joshajohnson/entropy/mechanicals/entropy-case-0.3/plate.dxf

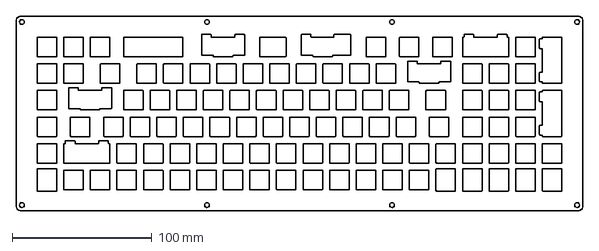
[picture p26: CAD file, 2021-12-18]
mechanicals/entropy-case-0.3/plate.dxf
405.9 x 139.3 mm
