joshajohnson/entropy/mechanicals/entropy-case-0.3/plate+1.dxf

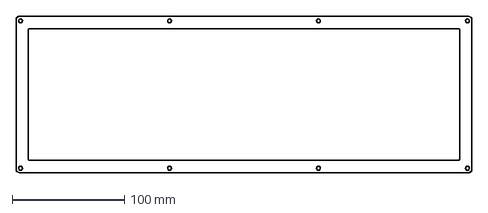
[picture p27: CAD file, 2021-12-18]
mechanicals/entropy-case-0.3/plate+1.dxf
405.9 x 139.3 mm
