joshajohnson/entropy/hardware/0.1/keyboard.sch

## KiCad design hardware/0.1/keyboard.sch (2020-07-07)

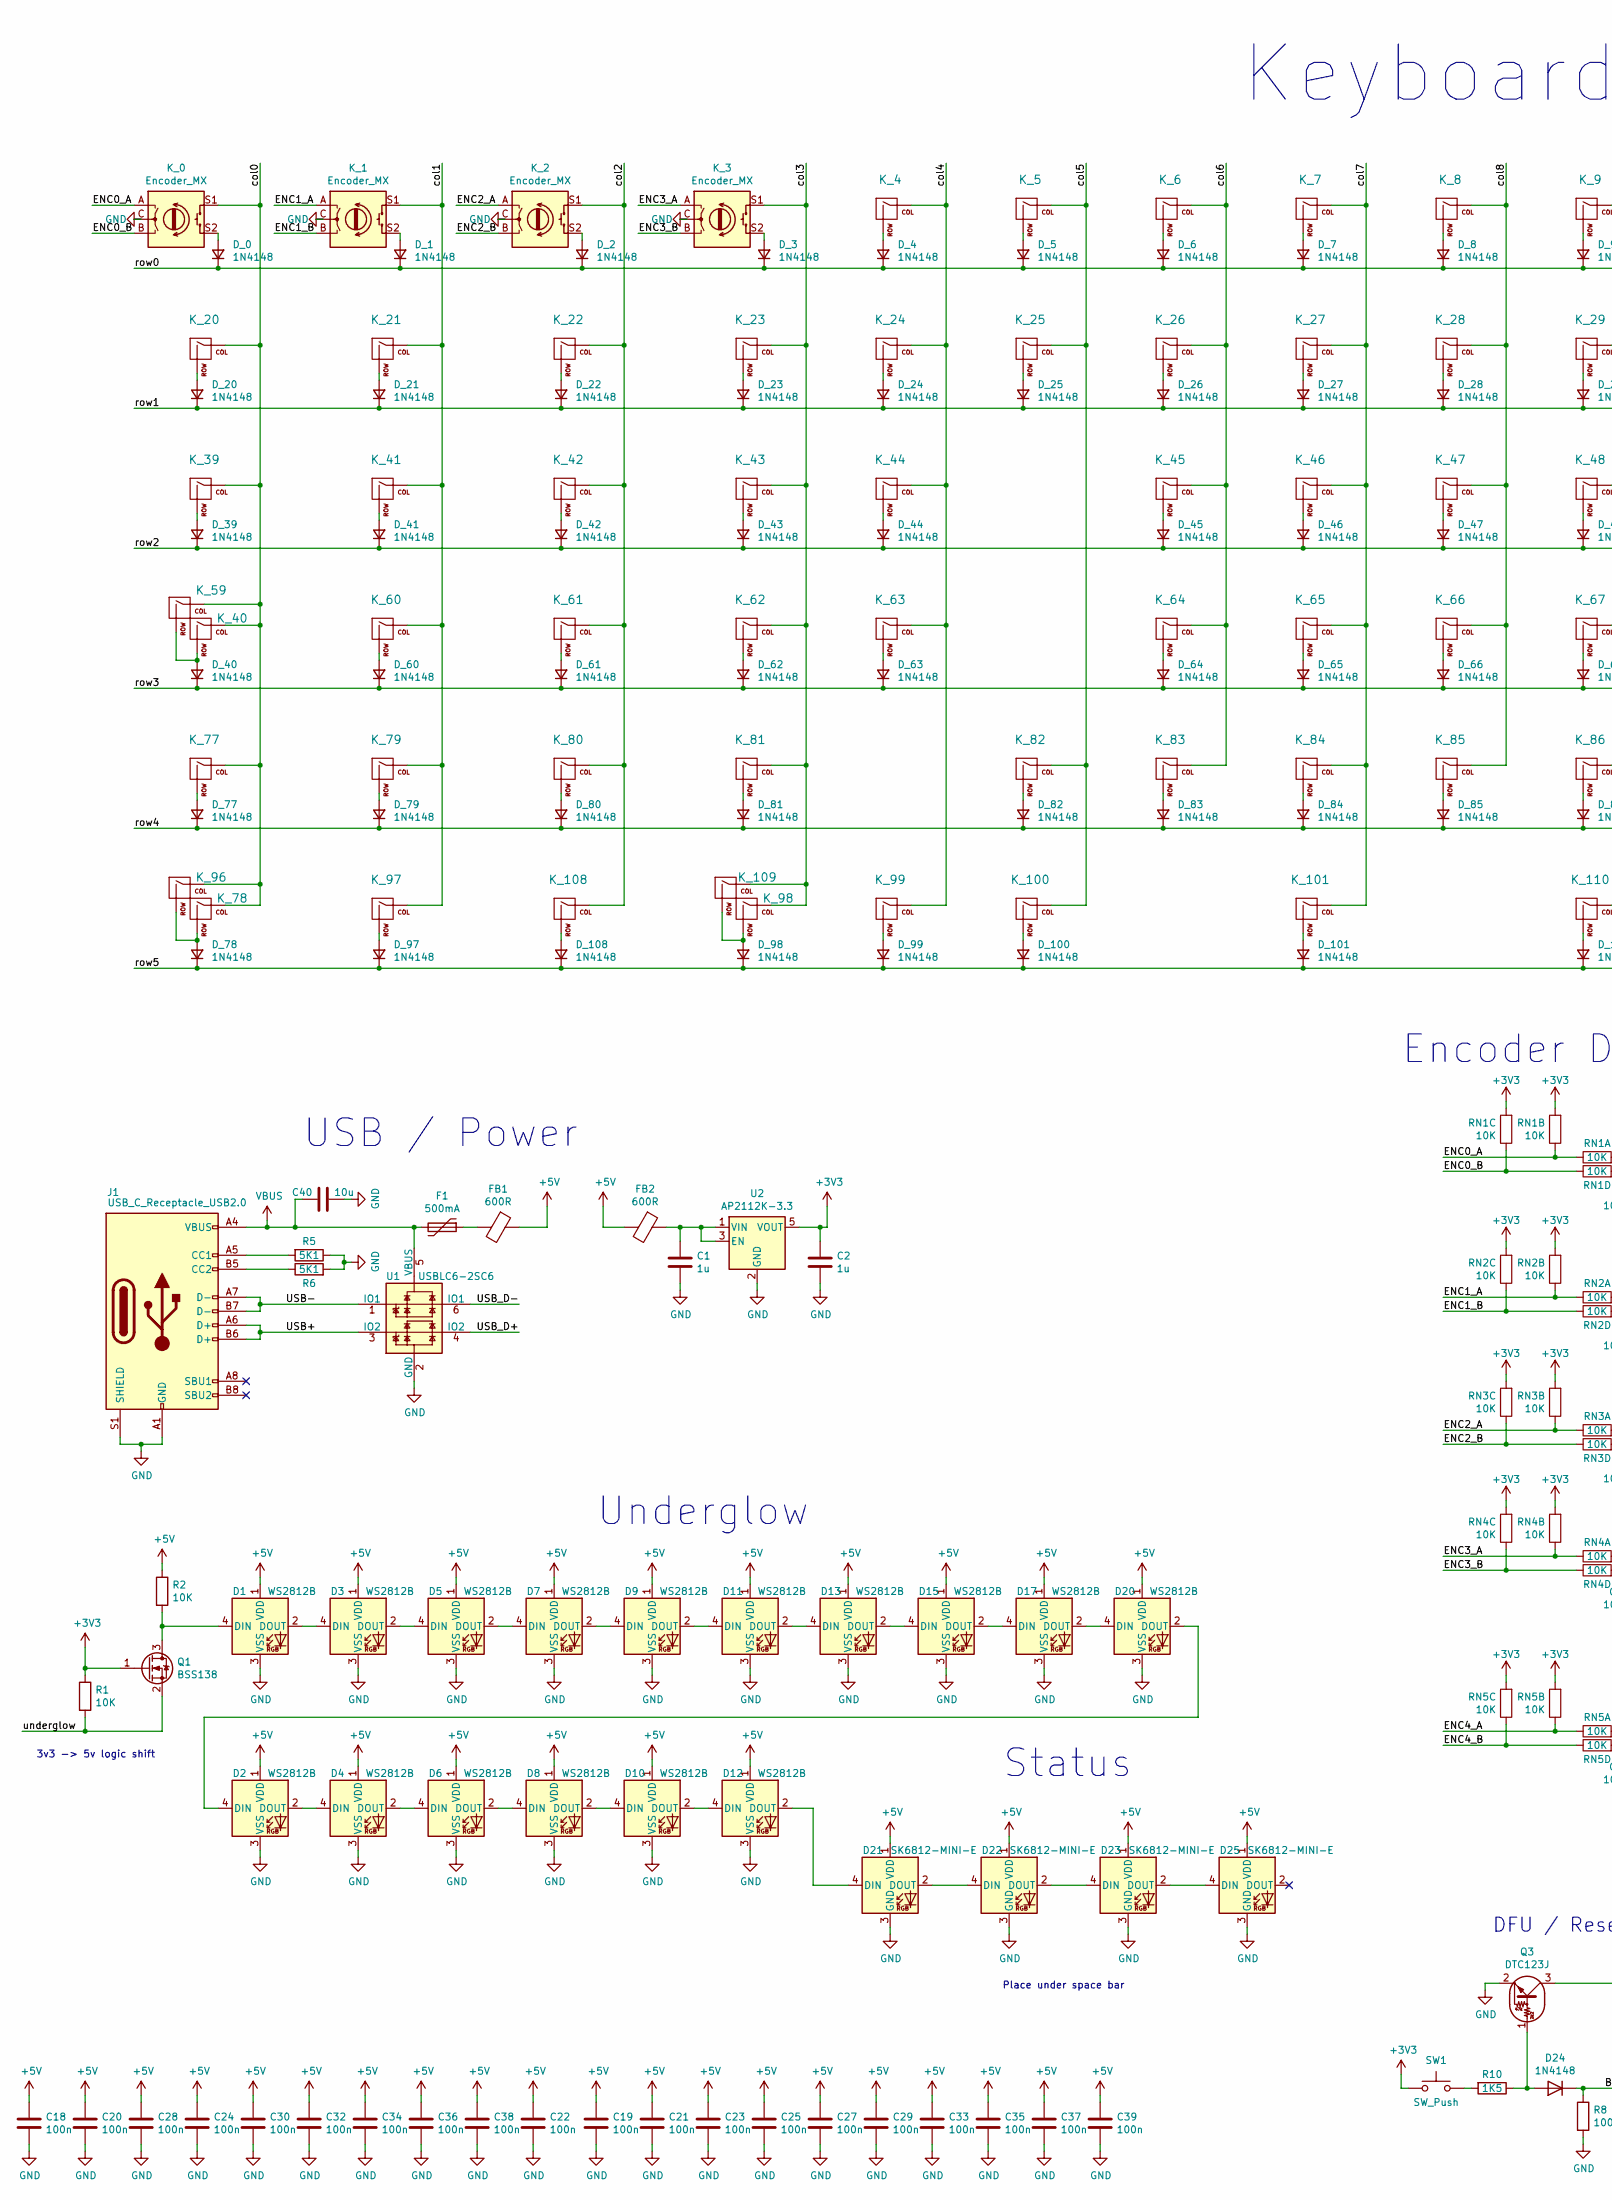
[picture p30: schematic keyboard.sch, part in row 1, column 1]

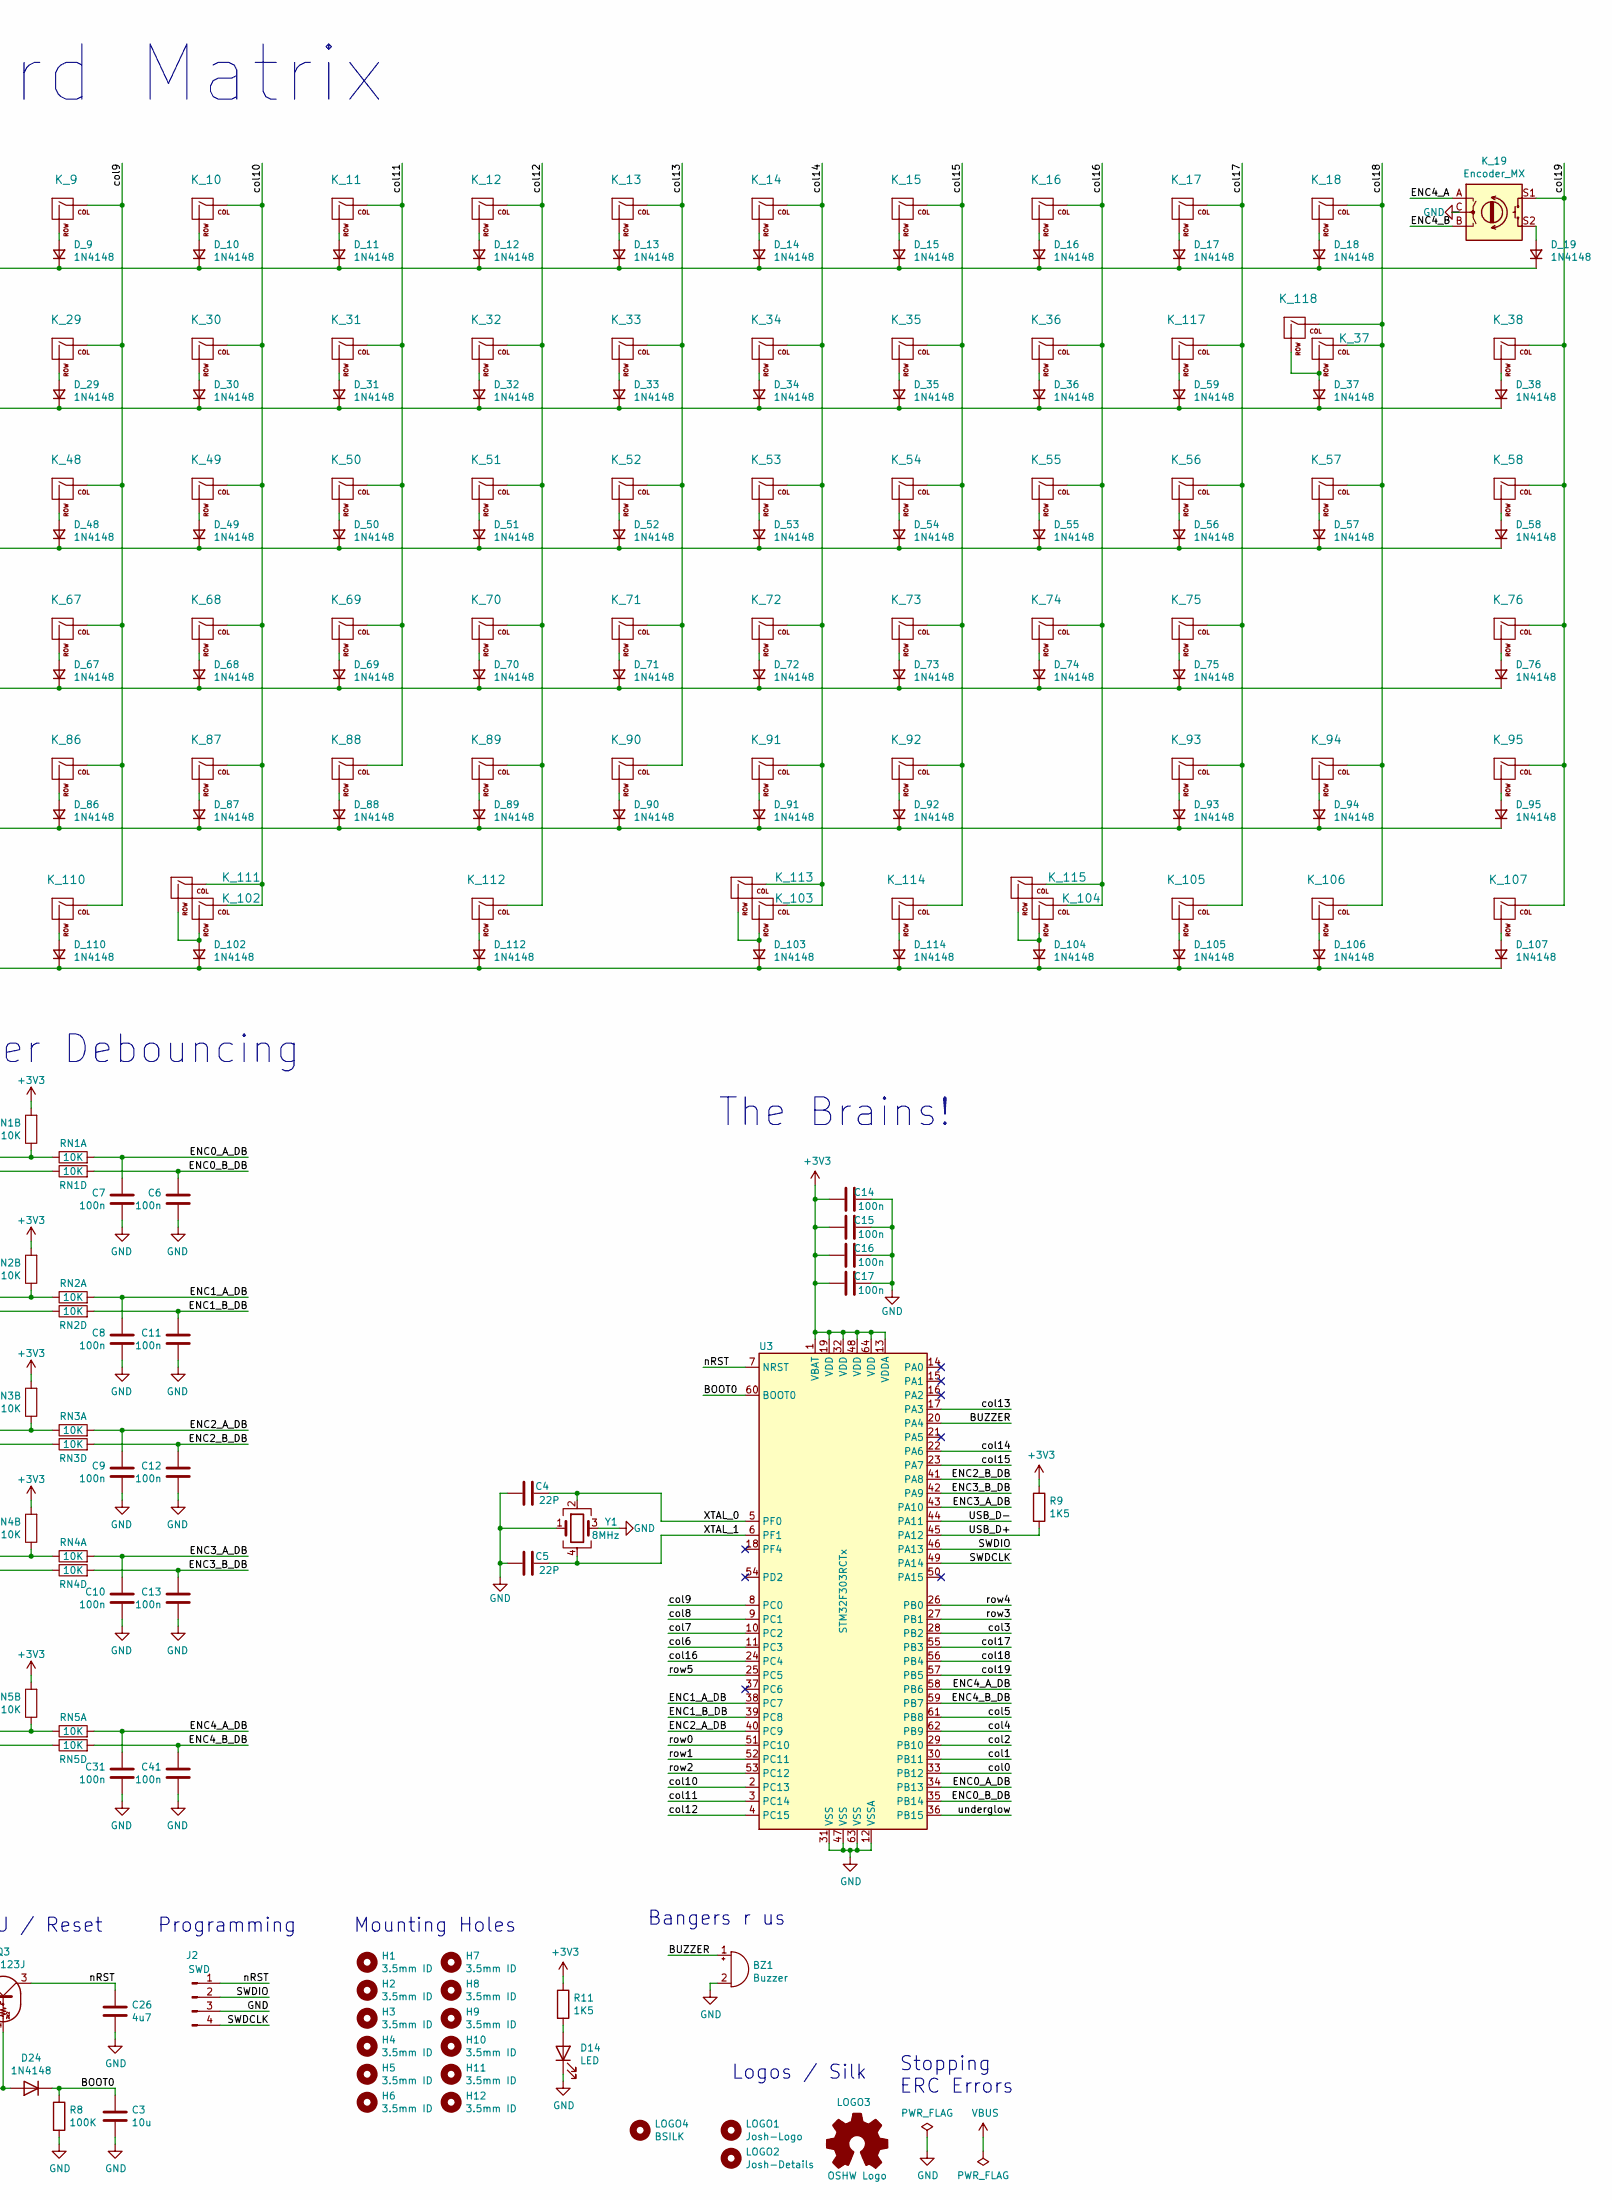
[picture p31: schematic keyboard.sch, part in row 1, column 2]

Parts:
BZ1: Buzzer; Buzzer_Murata_PKMCS0909E4000-R1
C1, C2: 1u; C_0603_1608Metric; MPN CL10A105MP8NNNC; LCSC C15849
C3, C40: 10u; C_0603_1608Metric; JLCSMT 1740133
C4, C5: 22P; C_0603_1608Metric; MPN CL10C220JB8NNNC; JLCSMT C1653
C6, C7, C8, C9, C10, C11, C12, C13, C14, C15, C16, C17, C31, C41: 100n; C_0603_1608Metric; MPN CC0603KRX7R9BB104; JLCSMT C14663
C18, C19, C20, C21, C22, C23, C24, C25, C27, C28, C29, C30, C32, C33, C34, C35, C36, C37, C38, C39: 100n; C_0603_1608Metric; MPN CC0603KRX7R9BB104; LCSC C14663
C26: 4u7; C_0603_1608Metric; MPN CL10A475KO8NNNC; JLCSMT C19666
D1, D2, D3, D4, D5, D6, D7, D8, D9, D10, D11, D12, D13, D15, D17, D20: WS2812B; LED_WS2812B_PLCC4_5.0x5.0mm_P3.2mm; MPN WS2812B-B; DigiKey 1528-1104-ND
D14: LED; LED_0603_1608Metric
D21, D22, D23, D25: SK6812-MINI-E; SK8612-MINI-E
D24: 1N4148; D_SOD-123; MPN 1N4148W; JLCSMT C81598
D_0, D_1, D_2, D_3, D_4, D_5, D_6, D_7, D_8, D_9, D_10, D_11, D_12, D_13, D_14, D_15, D_16, D_17, D_18, D_19, D_20, D_21, D_22, D_23, D_24, D_25, D_26, D_27, D_28, D_29, D_30, D_31, D_32, D_33, D_34, D_35, D_36, D_37, D_38, D_39, D_40, D_41, D_42, D_43, D_44, D_45, D_46, D_47, D_48, D_49, D_50, D_51, D_52, D_53, D_54, D_55, D_56, D_57, D_58, D_59, D_60, D_61, D_62, D_63, D_64, D_65, D_66, D_67, D_68, D_69, D_70, D_71, D_72, D_73, D_74, D_75, D_76, D_77, D_78, D_79, D_80, D_81, D_82, D_83, D_84, D_85, D_86, D_87, D_88, D_89, D_90, D_91, D_92, D_93, D_94, D_95, D_97, D_98, D_99, D_100, D_101, D_102, D_103, D_104, D_105, D_106, D_107, D_108, D_110, D_112, D_114: 1N4148; D_SOD-123; MPN 1N4148W; JLCSMT C81598
F1: 500mA; Fuse_0805_2012Metric
FB1, FB2: 600R; Ferrite_Bead_0603
H1, H2, H3, H4, H5, H6, H7, H8, H9, H10, H11, H12: 3.5mm ID; MountingHole_3.5mm
J1: USB_C_Receptacle_USB2.0; USB_C_U262-161N-4BVC11; MPN U262-161N-4BVC11; LCSC C319148
J2: SWD; STM_4_PIN_THT_Staggered
K_0, K_1, K_2, K_3, K_19: Encoder_MX; MX_KEYSWITCH_ENCODER
K_4, K_5, K_6, K_7, K_8, K_9, K_10, K_11, K_12, K_13, K_14, K_15, K_16, K_17, K_18, K_20, K_21, K_22, K_23, K_24, K_25, K_26, K_27, K_28, K_29, K_30, K_31, K_32, K_33, K_34, K_35, K_36, K_38, K_39, K_41, K_42, K_43, K_45, K_46, K_47, K_48, K_49, K_50, K_51, K_52, K_53, K_54, K_55, K_56, K_58, K_59, K_60, K_61, K_62, K_64, K_65, K_66, K_67, K_68, K_69, K_70, K_71, K_72, K_73, K_74, K_76, K_77, K_79, K_80, K_81, K_83, K_84, K_85, K_86, K_87, K_88, K_89, K_90, K_91, K_92, K_94, K_95, K_96, K_97, K_105, K_106, K_107, K_108, K_109, K_113, K_114, K_115, K_117, K_118: KEYSW; MXOnly-1U-NoLED
K_37, K_40, K_78: KEYSW; MXOnly-2U-NoLED
K_44, K_57, K_103, K_104: KEYSW; MXOnly-1.5U-NoLED
K_63, K_93: KEYSW; MXOnly-1.75U-NoLED
K_75, K_82, K_112: KEYSW; MXOnly-2.25U-ReversedStabilizers-NoLED
K_98: KEYSW; MXOnly-2U-ReversedStabilizers-NoLED
K_99, K_100, K_101, K_111: KEYSW; MXOnly-1.25U-NoLED
K_102: KEYSW; MXOnly-6.25U-ReversedStabilizers-NoLED
K_110: KEYSW; MXOnly-2.75U-ReversedStabilizers-NoLED
LOGO1: Josh-Logo; josh-johnson-logo-17x3
LOGO2: Josh-Details; josh-details
LOGO3: OSHW Logo; OSHW_Logo_3.6x3.6_F.Mask
LOGO4: BSILK; back_silk_v0
Q1: BSS138; SOT-23; MPN BSS138P,215; LCSC C75547
Q3: DTC123J; SOT-23
R1, R2: 10K; R_0603_1608Metric; MPN 0603WAF1002T5E; LCSC C25804
R5, R6: 5K1; R_0603_1608Metric; MPN 0603WAF5101T5E; JLCSMT C23186
R8: 100K; R_0603_1608Metric; MPN 0603WAF1003T5E; JLCSMT C25803
R9, R10, R11: 1K5; R_0603_1608Metric; MPN 0603WAF1501T5E; JLCSMT C22843
RN1, RN2, RN3, RN4, RN5: 10K; R_Array_Convex_4x0603; MPN 4D03WGJ0103T5E; JLCSMT C29718
SW1: SW_Push; Panasonic_EVQPUL_EVQPUC
U1: USBLC6-2SC6; SOT-23-6
U2: AP2112K-3.3; SOT-23-5; MPN AP2112K-3.3TRG1; LCSC C51118
U3: STM32F303RCTx; LQFP-64_10x10mm_P0.5mm; MPN STM32F303RCT6; JLCSMT C65361
Y1: 8MHz; Crystal_SMD_3225-4Pin_3.2x2.5mm

Connections:
+3V3: C2.2, C14.2, C15.2, C16.2, C17.2, Q1.1 (G), R1.1, R9.1, R11.1, RN1.2, RN1.3, RN2.2, RN2.3, RN3.2, RN3.3, RN4.2, RN4.3, RN5.2, RN5.3, SW1.1, U2.5 (VOUT), U3.1 (VBAT), U3.13 (VDDA), U3.19 (VDD), U3.32 (VDD), U3.48 (VDD), U3.64 (VDD)
+5V: C18.2, C19.2, C20.2, C21.2, C22.2, C23.2, C24.2, C25.2, C27.2, C28.2, C29.2, C30.2, C32.2, C33.2, C34.2, C35.2, C36.2, C37.2, C38.2, C39.2, D1.1 (VDD), D2.1 (VDD), D3.1 (VDD), D4.1 (VDD), D5.1 (VDD), D6.1 (VDD), D7.1 (VDD), D8.1 (VDD), D9.1 (VDD), D10.1 (VDD), D11.1 (VDD), D12.1 (VDD), D13.1 (VDD), D15.1 (VDD), D17.1 (VDD), D20.1 (VDD), D21.1 (VDD), D22.1 (VDD), D23.1 (VDD), D25.1 (VDD), FB1.1, FB2.2, R2.1
BOOT0: C3.1, D24.1 (K), R8.1, U3.60 (BOOT0)
BUZZER: BZ1.1 (-), U3.20 (PA4)
ENC0_A: K_0.A, RN1.5, RN1.6
ENC0_A_DB: C7.1, RN1.4, U3.34 (PB13)
ENC0_B: K_0.B, RN1.7, RN1.8
ENC0_B_DB: C6.1, RN1.1, U3.35 (PB14)
ENC1_A: K_1.A, RN2.5, RN2.6
ENC1_A_DB: C8.1, RN2.4, U3.38 (PC7)
ENC1_B: K_1.B, RN2.7, RN2.8
ENC1_B_DB: C11.1, RN2.1, U3.39 (PC8)
ENC2_A: K_2.A, RN3.5, RN3.6
ENC2_A_DB: C9.1, RN3.4, U3.40 (PC9)
ENC2_B: K_2.B, RN3.7, RN3.8
ENC2_B_DB: C12.1, RN3.1, U3.41 (PA8)
ENC3_A: K_3.A, RN4.5, RN4.6
ENC3_A_DB: C10.1, RN4.4, U3.43 (PA10)
ENC3_B: K_3.B, RN4.7, RN4.8
ENC3_B_DB: C13.1, RN4.1, U3.42 (PA9)
ENC4_A: K_19.A, RN5.5, RN5.6
ENC4_A_DB: C31.1, RN5.4, U3.58 (PB6)
ENC4_B: K_19.B, RN5.7, RN5.8
ENC4_B_DB: C41.1, RN5.1, U3.59 (PB7)
GND: BZ1.2 (+), C1.1, C2.1, C3.2, C4.2, C5.2, C6.2, C7.2, C8.2, C9.2, C10.2, C11.2, C12.2, C13.2, C14.1, C15.1, C16.1, C17.1, C18.1, C19.1, C20.1, C21.1, C22.1, C23.1, C24.1, C25.1, C26.2, C27.1, C28.1, C29.1, C30.1, C31.2, C32.1, C33.1, C34.1, C35.1, C36.1, C37.1, C38.1, C39.1, C40.1, C41.2, D1.3 (VSS), D2.3 (VSS), D3.3 (VSS), D4.3 (VSS), D5.3 (VSS), D6.3 (VSS), D7.3 (VSS), D8.3 (VSS), D9.3 (VSS), D10.3 (VSS), D11.3 (VSS), D12.3 (VSS), D13.3 (VSS), D14.1 (K), D15.3 (VSS), D17.3 (VSS), D20.3 (VSS), D21.3 (GND), D22.3 (GND), D23.3 (GND), D25.3 (GND), J1.A1 (GND), J1.A12 (GND), J1.B1 (GND), J1.B12 (GND), J1.S1 (SHIELD), J2.3, K_0.C, K_1.C, K_2.C, K_3.C, K_19.C, Q3.2 (E), R5.1, R6.2, R8.2, U1.2 (GND), U2.2 (GND), U3.12 (VSSA), U3.31 (VSS), U3.47 (VSS), U3.63 (VSS), Y1.1, Y1.3
unnamed: C1.2, FB2.1, U2.1 (VIN), U2.3 (EN)
unnamed: D1.2 (DOUT), D3.4 (DIN)
unnamed: D1.4 (DIN), Q1.3 (D), R2.2
unnamed: D2.2 (DOUT), D4.4 (DIN)
unnamed: D2.4 (DIN), D20.2 (DOUT)
unnamed: D3.2 (DOUT), D5.4 (DIN)
unnamed: D4.2 (DOUT), D6.4 (DIN)
unnamed: D5.2 (DOUT), D7.4 (DIN)
unnamed: D6.2 (DOUT), D8.4 (DIN)
unnamed: D7.2 (DOUT), D9.4 (DIN)
unnamed: D10.2 (DOUT), D12.4 (DIN)
unnamed: D8.2 (DOUT), D10.4 (DIN)
unnamed: D11.2 (DOUT), D13.4 (DIN)
unnamed: D9.2 (DOUT), D11.4 (DIN)
unnamed: D12.2 (DOUT), D21.4 (DIN)
unnamed: D13.2 (DOUT), D15.4 (DIN)
unnamed: D14.2 (A), R11.2
unnamed: D15.2 (DOUT), D17.4 (DIN)
unnamed: D17.2 (DOUT), D20.4 (DIN)
unnamed: D21.2 (DOUT), D22.4 (DIN)
unnamed: D22.2 (DOUT), D23.4 (DIN)
unnamed: D23.2 (DOUT), D25.4 (DIN)
unnamed: D24.2 (A), Q3.1 (B), R10.1
unnamed: D_0.2 (A), K_0.S2
unnamed: D_1.2 (A), K_1.S2
unnamed: D_2.2 (A), K_2.S2
unnamed: D_3.2 (A), K_3.S2
unnamed: D_4.2 (A), K_4.2 (ROW)
unnamed: D_5.2 (A), K_5.2 (ROW)
unnamed: D_6.2 (A), K_6.2 (ROW)
unnamed: D_7.2 (A), K_7.2 (ROW)
unnamed: D_8.2 (A), K_8.2 (ROW)
unnamed: D_9.2 (A), K_9.2 (ROW)
unnamed: D_10.2 (A), K_10.2 (ROW)
unnamed: D_11.2 (A), K_11.2 (ROW)
unnamed: D_12.2 (A), K_12.2 (ROW)
unnamed: D_13.2 (A), K_13.2 (ROW)
unnamed: D_14.2 (A), K_14.2 (ROW)
unnamed: D_15.2 (A), K_15.2 (ROW)
unnamed: D_16.2 (A), K_16.2 (ROW)
unnamed: D_17.2 (A), K_17.2 (ROW)
unnamed: D_18.2 (A), K_18.2 (ROW)
unnamed: D_19.2 (A), K_19.S2
unnamed: D_20.2 (A), K_20.2 (ROW)
unnamed: D_21.2 (A), K_21.2 (ROW)
unnamed: D_22.2 (A), K_22.2 (ROW)
unnamed: D_23.2 (A), K_23.2 (ROW)
unnamed: D_24.2 (A), K_24.2 (ROW)
unnamed: D_25.2 (A), K_25.2 (ROW)
unnamed: D_26.2 (A), K_26.2 (ROW)
unnamed: D_27.2 (A), K_27.2 (ROW)
unnamed: D_28.2 (A), K_28.2 (ROW)
unnamed: D_29.2 (A), K_29.2 (ROW)
unnamed: D_30.2 (A), K_30.2 (ROW)
unnamed: D_31.2 (A), K_31.2 (ROW)
unnamed: D_32.2 (A), K_32.2 (ROW)
unnamed: D_33.2 (A), K_33.2 (ROW)
unnamed: D_34.2 (A), K_34.2 (ROW)
unnamed: D_35.2 (A), K_35.2 (ROW)
unnamed: D_36.2 (A), K_36.2 (ROW)
unnamed: D_37.2 (A), K_37.2 (ROW), K_118.2 (ROW)
unnamed: D_38.2 (A), K_38.2 (ROW)
unnamed: D_39.2 (A), K_39.2 (ROW)
unnamed: D_40.2 (A), K_40.2 (ROW), K_59.2 (ROW)
unnamed: D_41.2 (A), K_41.2 (ROW)
unnamed: D_42.2 (A), K_42.2 (ROW)
unnamed: D_43.2 (A), K_43.2 (ROW)
unnamed: D_44.2 (A), K_44.2 (ROW)
unnamed: D_45.2 (A), K_45.2 (ROW)
unnamed: D_46.2 (A), K_46.2 (ROW)
unnamed: D_47.2 (A), K_47.2 (ROW)
unnamed: D_48.2 (A), K_48.2 (ROW)
unnamed: D_49.2 (A), K_49.2 (ROW)
unnamed: D_50.2 (A), K_50.2 (ROW)
unnamed: D_51.2 (A), K_51.2 (ROW)
unnamed: D_52.2 (A), K_52.2 (ROW)
unnamed: D_53.2 (A), K_53.2 (ROW)
unnamed: D_54.2 (A), K_54.2 (ROW)
unnamed: D_55.2 (A), K_55.2 (ROW)
unnamed: D_56.2 (A), K_56.2 (ROW)
unnamed: D_57.2 (A), K_57.2 (ROW)
unnamed: D_58.2 (A), K_58.2 (ROW)
unnamed: D_59.2 (A), K_117.2 (ROW)
unnamed: D_60.2 (A), K_60.2 (ROW)
unnamed: D_61.2 (A), K_61.2 (ROW)
unnamed: D_62.2 (A), K_62.2 (ROW)
unnamed: D_63.2 (A), K_63.2 (ROW)
unnamed: D_64.2 (A), K_64.2 (ROW)
unnamed: D_65.2 (A), K_65.2 (ROW)
unnamed: D_66.2 (A), K_66.2 (ROW)
unnamed: D_67.2 (A), K_67.2 (ROW)
unnamed: D_68.2 (A), K_68.2 (ROW)
unnamed: D_69.2 (A), K_69.2 (ROW)
unnamed: D_70.2 (A), K_70.2 (ROW)
unnamed: D_71.2 (A), K_71.2 (ROW)
unnamed: D_72.2 (A), K_72.2 (ROW)
unnamed: D_73.2 (A), K_73.2 (ROW)
unnamed: D_74.2 (A), K_74.2 (ROW)
unnamed: D_75.2 (A), K_75.2 (ROW)
unnamed: D_76.2 (A), K_76.2 (ROW)
unnamed: D_77.2 (A), K_77.2 (ROW)
unnamed: D_78.2 (A), K_78.2 (ROW), K_96.2 (ROW)
unnamed: D_79.2 (A), K_79.2 (ROW)
unnamed: D_80.2 (A), K_80.2 (ROW)
unnamed: D_81.2 (A), K_81.2 (ROW)
unnamed: D_82.2 (A), K_82.2 (ROW)
unnamed: D_83.2 (A), K_83.2 (ROW)
unnamed: D_84.2 (A), K_84.2 (ROW)
unnamed: D_85.2 (A), K_85.2 (ROW)
unnamed: D_86.2 (A), K_86.2 (ROW)
unnamed: D_87.2 (A), K_87.2 (ROW)
unnamed: D_88.2 (A), K_88.2 (ROW)
unnamed: D_89.2 (A), K_89.2 (ROW)
unnamed: D_90.2 (A), K_90.2 (ROW)
unnamed: D_91.2 (A), K_91.2 (ROW)
unnamed: D_92.2 (A), K_92.2 (ROW)
unnamed: D_93.2 (A), K_93.2 (ROW)
unnamed: D_94.2 (A), K_94.2 (ROW)
unnamed: D_95.2 (A), K_95.2 (ROW)
unnamed: D_97.2 (A), K_97.2 (ROW)
unnamed: D_98.2 (A), K_98.2 (ROW), K_109.2 (ROW)
unnamed: D_99.2 (A), K_99.2 (ROW)
unnamed: D_100.2 (A), K_100.2 (ROW)
unnamed: D_101.2 (A), K_101.2 (ROW)
unnamed: D_102.2 (A), K_102.2 (ROW), K_111.2 (ROW)
unnamed: D_103.2 (A), K_103.2 (ROW), K_113.2 (ROW)
unnamed: D_104.2 (A), K_104.2 (ROW), K_115.2 (ROW)
unnamed: D_105.2 (A), K_105.2 (ROW)
unnamed: D_106.2 (A), K_106.2 (ROW)
unnamed: D_107.2 (A), K_107.2 (ROW)
unnamed: D_108.2 (A), K_108.2 (ROW)
unnamed: D_110.2 (A), K_110.2 (ROW)
unnamed: D_112.2 (A), K_112.2 (ROW)
unnamed: D_114.2 (A), K_114.2 (ROW)
unnamed: F1.1, FB1.2
unnamed: J1.A5 (CC1), R5.2
unnamed: J1.B5 (CC2), R6.1
unnamed: R10.2, SW1.2
SWDCLK: J2.4, U3.49 (PA14)
SWDIO: J2.2, U3.46 (PA13)
USB+: J1.A6 (D+), J1.B6 (D+), U1.3 (IO2)
USB-: J1.A7 (D-), J1.B7 (D-), U1.1 (IO1)
USB_D+: R9.2, U1.4 (IO2), U3.45 (PA12)
USB_D-: U1.6 (IO1), U3.44 (PA11)
VBUS: C40.2, F1.2, J1.A4 (VBUS), J1.A9 (VBUS), J1.B4 (VBUS), J1.B9 (VBUS), U1.5 (VBUS)
XTAL_0: C4.1, U3.5 (PF0), Y1.2
XTAL_1: C5.1, U3.6 (PF1), Y1.4
col0: K_0.S1, K_20.1 (COL), K_39.1 (COL), K_40.1 (COL), K_59.1 (COL), K_77.1 (COL), K_78.1 (COL), K_96.1 (COL), U3.33 (PB12)
col1: K_1.S1, K_21.1 (COL), K_41.1 (COL), K_60.1 (COL), K_79.1 (COL), K_97.1 (COL), U3.30 (PB11)
col2: K_2.S1, K_22.1 (COL), K_42.1 (COL), K_61.1 (COL), K_80.1 (COL), K_108.1 (COL), U3.29 (PB10)
col3: K_3.S1, K_23.1 (COL), K_43.1 (COL), K_62.1 (COL), K_81.1 (COL), K_98.1 (COL), K_109.1 (COL), U3.28 (PB2)
col4: K_4.1 (COL), K_24.1 (COL), K_44.1 (COL), K_63.1 (COL), K_99.1 (COL), U3.62 (PB9)
col5: K_5.1 (COL), K_25.1 (COL), K_82.1 (COL), K_100.1 (COL), U3.61 (PB8)
col6: K_6.1 (COL), K_26.1 (COL), K_45.1 (COL), K_64.1 (COL), K_83.1 (COL), U3.11 (PC3)
col7: K_7.1 (COL), K_27.1 (COL), K_46.1 (COL), K_65.1 (COL), K_84.1 (COL), K_101.1 (COL), U3.10 (PC2)
col8: K_8.1 (COL), K_28.1 (COL), K_47.1 (COL), K_66.1 (COL), K_85.1 (COL), U3.9 (PC1)
col9: K_9.1 (COL), K_29.1 (COL), K_48.1 (COL), K_67.1 (COL), K_86.1 (COL), K_110.1 (COL), U3.8 (PC0)
col10: K_10.1 (COL), K_30.1 (COL), K_49.1 (COL), K_68.1 (COL), K_87.1 (COL), K_102.1 (COL), K_111.1 (COL), U3.2 (PC13)
col11: K_11.1 (COL), K_31.1 (COL), K_50.1 (COL), K_69.1 (COL), K_88.1 (COL), U3.3 (PC14)
col12: K_12.1 (COL), K_32.1 (COL), K_51.1 (COL), K_70.1 (COL), K_89.1 (COL), K_112.1 (COL), U3.4 (PC15)
col13: K_13.1 (COL), K_33.1 (COL), K_52.1 (COL), K_71.1 (COL), K_90.1 (COL), U3.17 (PA3)
col14: K_14.1 (COL), K_34.1 (COL), K_53.1 (COL), K_72.1 (COL), K_91.1 (COL), K_103.1 (COL), K_113.1 (COL), U3.22 (PA6)
col15: K_15.1 (COL), K_35.1 (COL), K_54.1 (COL), K_73.1 (COL), K_92.1 (COL), K_114.1 (COL), U3.23 (PA7)
col16: K_16.1 (COL), K_36.1 (COL), K_55.1 (COL), K_74.1 (COL), K_104.1 (COL), K_115.1 (COL), U3.24 (PC4)
col17: K_17.1 (COL), K_56.1 (COL), K_75.1 (COL), K_93.1 (COL), K_105.1 (COL), K_117.1 (COL), U3.55 (PB3)
col18: K_18.1 (COL), K_37.1 (COL), K_57.1 (COL), K_94.1 (COL), K_106.1 (COL), K_118.1 (COL), U3.56 (PB4)
col19: K_19.S1, K_38.1 (COL), K_58.1 (COL), K_76.1 (COL), K_95.1 (COL), K_107.1 (COL), U3.57 (PB5)
nRST: C26.1, J2.1, Q3.3 (C), U3.7 (NRST)
row0: D_0.1 (K), D_1.1 (K), D_2.1 (K), D_3.1 (K), D_4.1 (K), D_5.1 (K), D_6.1 (K), D_7.1 (K), D_8.1 (K), D_9.1 (K), D_10.1 (K), D_11.1 (K), D_12.1 (K), D_13.1 (K), D_14.1 (K), D_15.1 (K), D_16.1 (K), D_17.1 (K), D_18.1 (K), D_19.1 (K), U3.51 (PC10)
row1: D_20.1 (K), D_21.1 (K), D_22.1 (K), D_23.1 (K), D_24.1 (K), D_25.1 (K), D_26.1 (K), D_27.1 (K), D_28.1 (K), D_29.1 (K), D_30.1 (K), D_31.1 (K), D_32.1 (K), D_33.1 (K), D_34.1 (K), D_35.1 (K), D_36.1 (K), D_37.1 (K), D_38.1 (K), D_59.1 (K), U3.52 (PC11)
row2: D_39.1 (K), D_41.1 (K), D_42.1 (K), D_43.1 (K), D_44.1 (K), D_45.1 (K), D_46.1 (K), D_47.1 (K), D_48.1 (K), D_49.1 (K), D_50.1 (K), D_51.1 (K), D_52.1 (K), D_53.1 (K), D_54.1 (K), D_55.1 (K), D_56.1 (K), D_57.1 (K), D_58.1 (K), U3.53 (PC12)
row3: D_40.1 (K), D_60.1 (K), D_61.1 (K), D_62.1 (K), D_63.1 (K), D_64.1 (K), D_65.1 (K), D_66.1 (K), D_67.1 (K), D_68.1 (K), D_69.1 (K), D_70.1 (K), D_71.1 (K), D_72.1 (K), D_73.1 (K), D_74.1 (K), D_75.1 (K), D_76.1 (K), U3.27 (PB1)
row4: D_77.1 (K), D_79.1 (K), D_80.1 (K), D_81.1 (K), D_82.1 (K), D_83.1 (K), D_84.1 (K), D_85.1 (K), D_86.1 (K), D_87.1 (K), D_88.1 (K), D_89.1 (K), D_90.1 (K), D_91.1 (K), D_92.1 (K), D_93.1 (K), D_94.1 (K), D_95.1 (K), U3.26 (PB0)
row5: D_78.1 (K), D_97.1 (K), D_98.1 (K), D_99.1 (K), D_100.1 (K), D_101.1 (K), D_102.1 (K), D_103.1 (K), D_104.1 (K), D_105.1 (K), D_106.1 (K), D_107.1 (K), D_108.1 (K), D_110.1 (K), D_112.1 (K), D_114.1 (K), U3.25 (PC5)
underglow: Q1.2 (S), R1.2, U3.36 (PB15)

Notes on the sheet:
Stopping ERC Errors
Underglow
3v3 -> 5v logic shift
Logos / Silk
Keyboard Matrix
Status
DFU / Reset
Place under space bar
USB / Power
Programming
Encoder Debouncing
The Brains!
Mounting Holes
Bangers r us
