joshajohnson/entropy/hardware/0.4-w/keyboard.kicad_sch

## KiCad design hardware/0.4-w/keyboard.kicad_sch (2021-12-18)

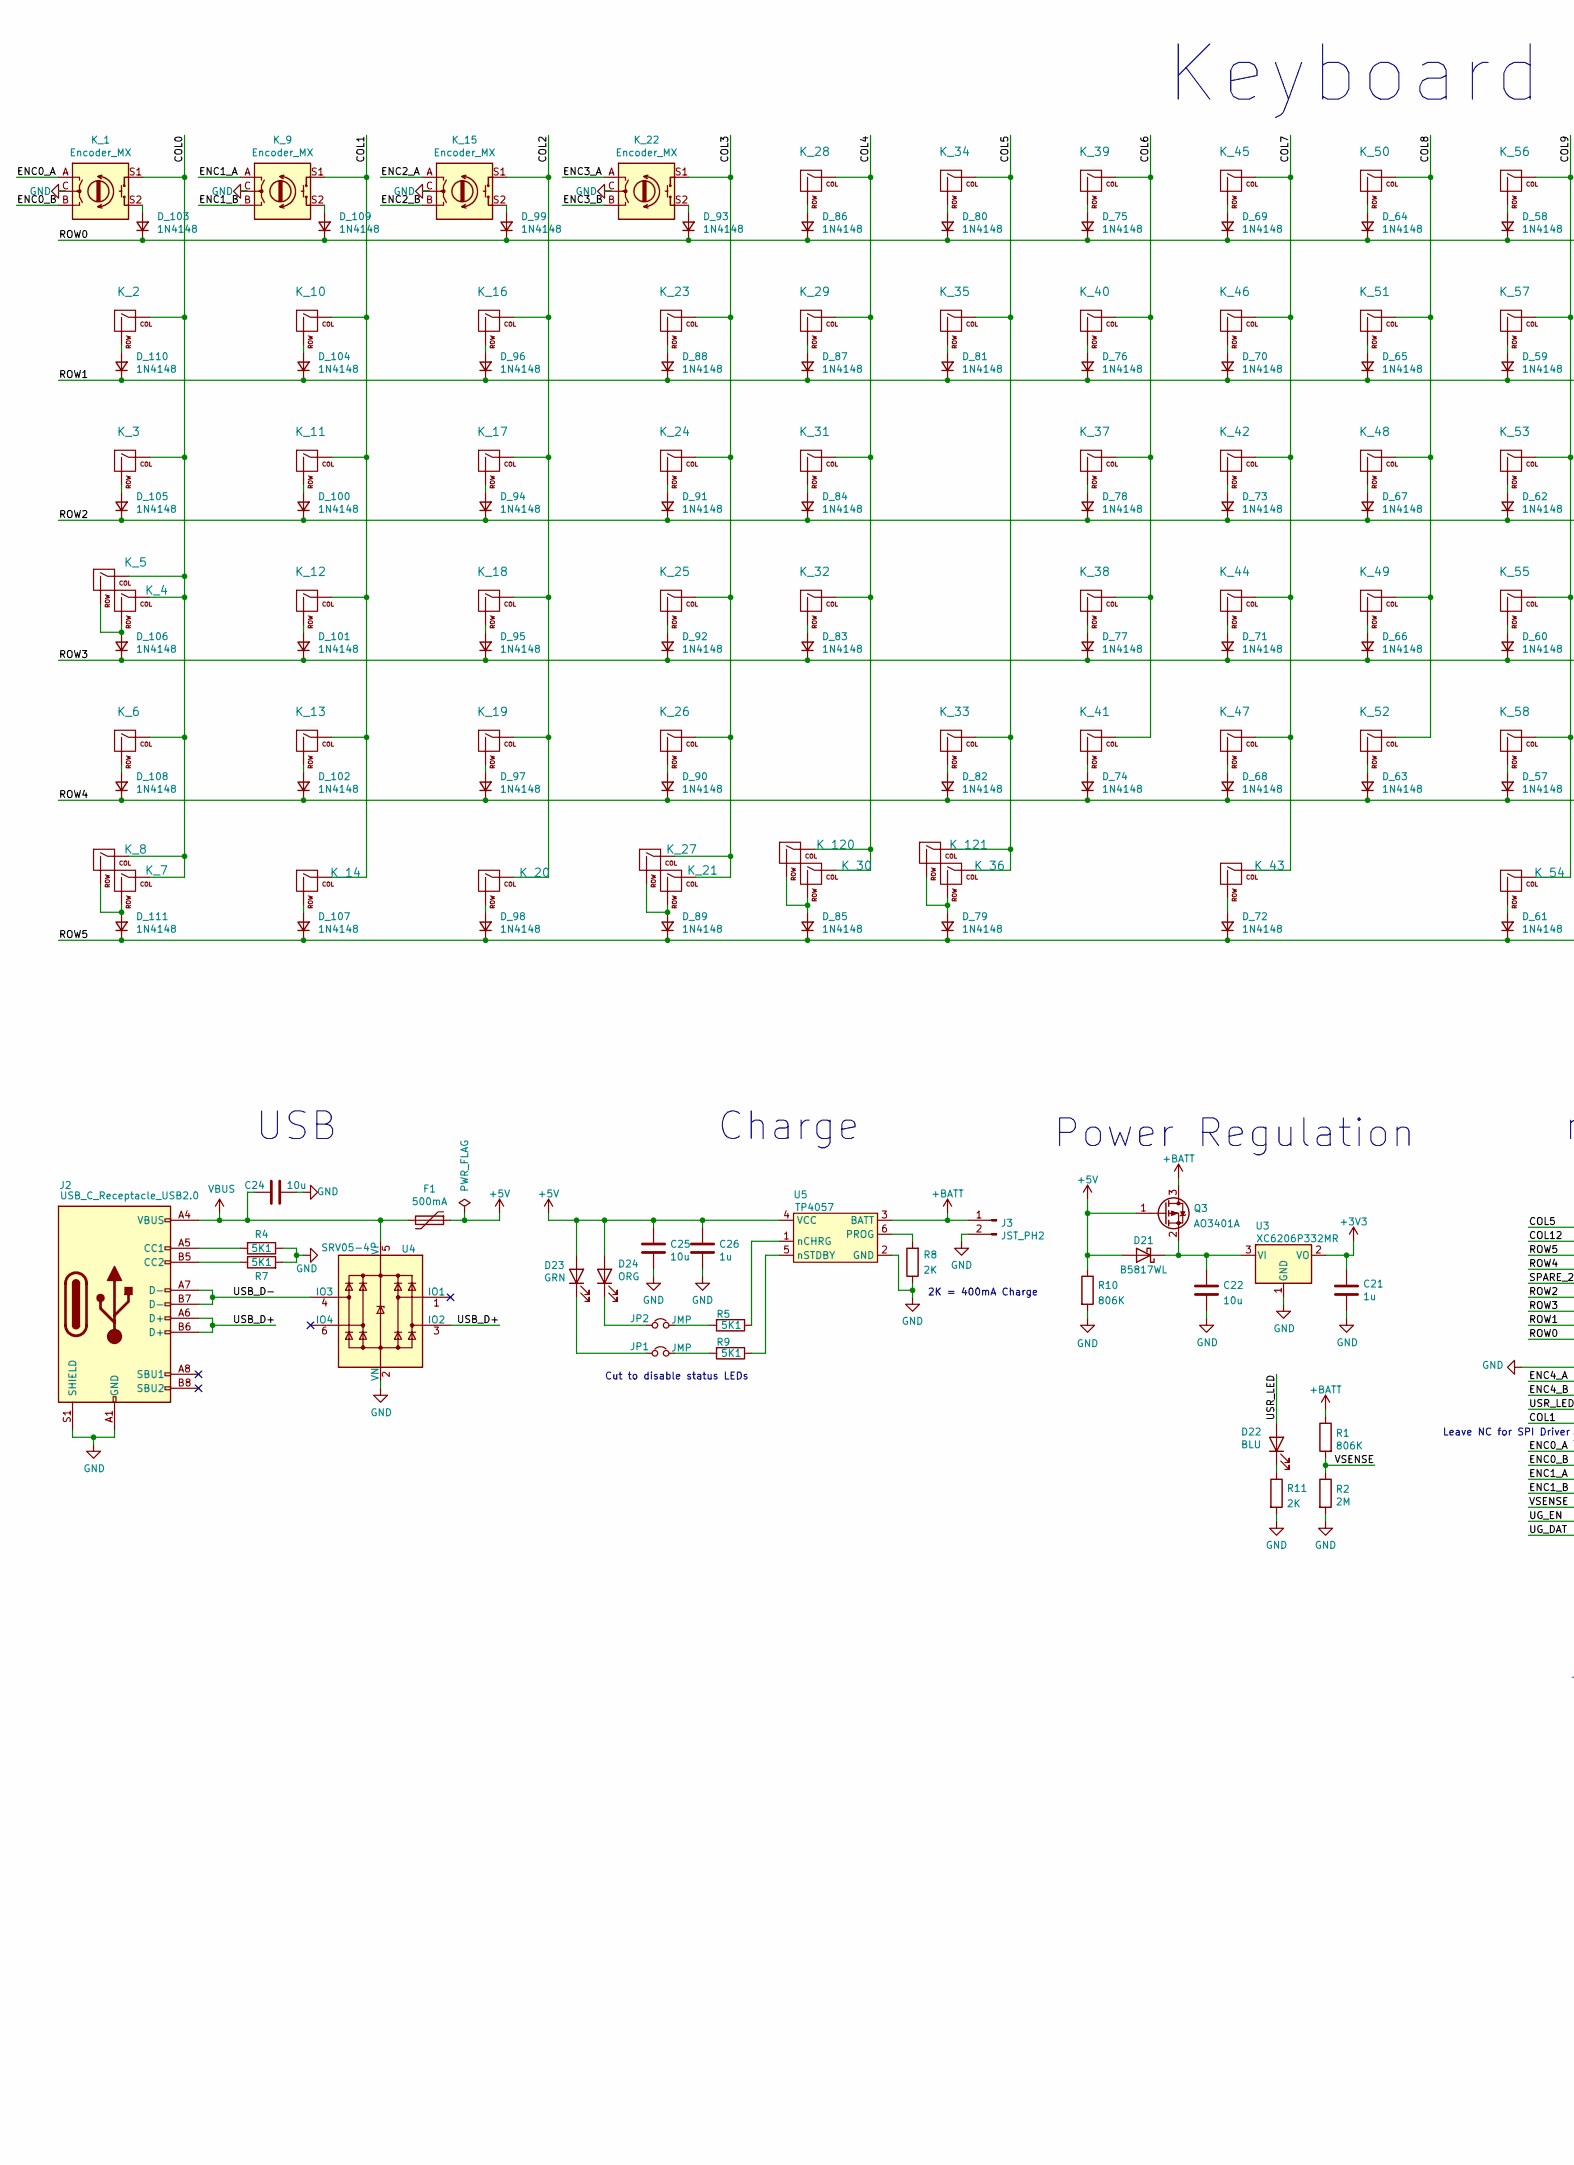
[picture p32: schematic keyboard.kicad_sch, part in row 1, column 1]

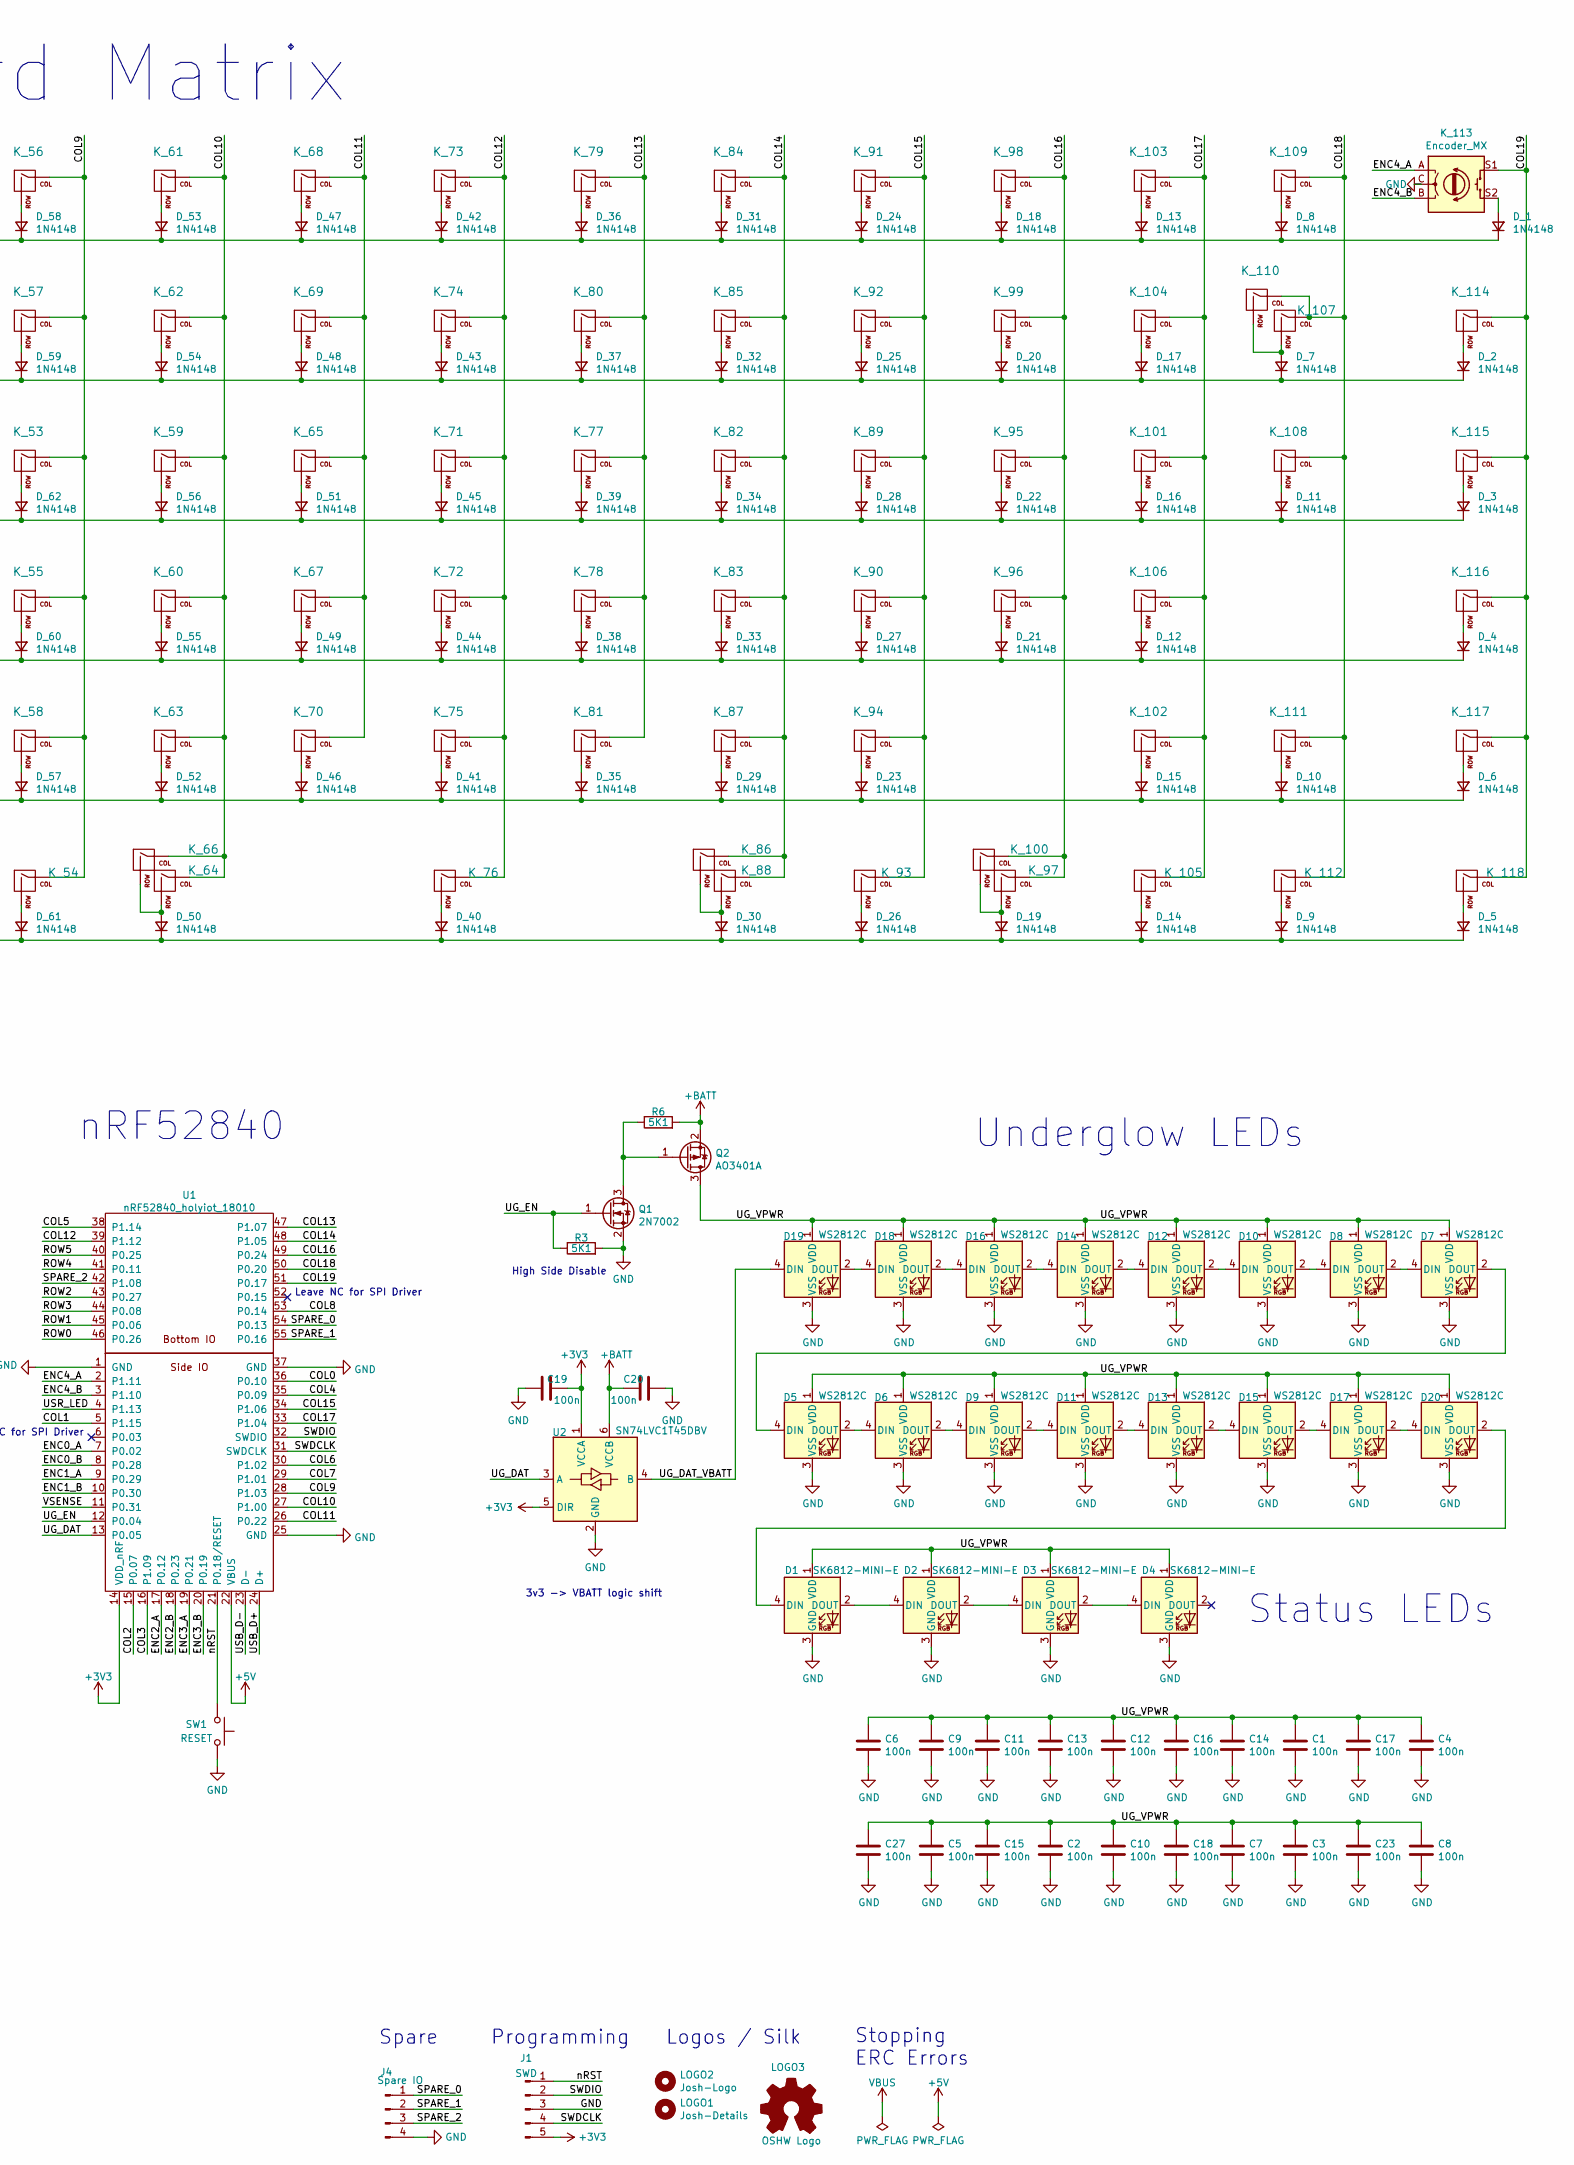
[picture p33: schematic keyboard.kicad_sch, part in row 1, column 2]

Parts:
C1, C2, C3, C4, C5, C6, C7, C8, C9, C10, C11, C12, C13, C14, C15, C16, C17, C18, C19, C20, C23, C27: 100n; C_0603_1608Metric; MPN CC0603KRX7R9BB104; LCSC C14663
C21: 1u; C_0603_1608Metric; MPN CL10A105KB8NNNC; LCSC C15849
C22, C24, C25: 10u; C_0603_1608Metric; MPN CL10A106KP8NNNC; JLCSMT C19702
C26: 1u; C_0603_1608Metric; MPN CL10A105KB8NNNC; JLCSMT C15849
D1, D2, D3, D4: SK6812-MINI-E; SK8612-MINI-E; MPN SK6812-MINI-E
D5, D6, D7, D8, D9, D10, D11, D12, D13, D14, D15, D16, D17, D18, D19, D20: WS2812C; LED_WS2812B_PLCC4_5.0x5.0mm_P3.2mm; MPN WS2812C; JLCSMT C114587
D21: B5817WL; D_SOD-123FL; MPN B5817WL; JLCSMT C122853
D22: BLU; LED_0603_1608Metric; MPN 19-217/BHC-ZL1M2RY/3T; JLCSMT C72041
D23: GRN; LED_0603_1608Metric; MPN 19-217/GHC-YR1S2/3T; JLCSMT C72043
D24: ORG; LED_0603_1608Metric; MPN KT-0603R; JLCSMT C2286
D_1, D_2, D_3, D_4, D_5, D_6, D_7, D_8, D_9, D_10, D_11, D_12, D_13, D_14, D_15, D_16, D_17, D_18, D_19, D_20, D_21, D_22, D_23, D_24, D_25, D_26, D_27, D_28, D_29, D_30, D_31, D_32, D_33, D_34, D_35, D_36, D_37, D_38, D_39, D_40, D_41, D_42, D_43, D_44, D_45, D_46, D_47, D_48, D_49, D_50, D_51, D_52, D_53, D_54, D_55, D_56, D_57, D_58, D_59, D_60, D_61, D_62, D_63, D_64, D_65, D_66, D_67, D_68, D_69, D_70, D_71, D_72, D_73, D_74, D_75, D_76, D_77, D_78, D_79, D_80, D_81, D_82, D_83, D_84, D_85, D_86, D_87, D_88, D_89, D_90, D_91, D_92, D_93, D_94, D_95, D_96, D_97, D_98, D_99, D_100, D_101, D_102, D_103, D_104, D_105, D_106, D_107, D_108, D_109, D_110, D_111: 1N4148; D_SOD-123; MPN 1N4148W; JLCSMT C81598
F1: 500mA; Fuse_0805_2012Metric; MPN SMD0805-050; JLCSMT C66452
J1: SWD; 5_PIN_THT_Staggered
J2: USB_C_Receptacle_USB2.0; USB_C_Receptacle_HRO_TYPE-C-31-M-12; MPN TYPE-C-31-M-12; LCSC C165948
J3: JST_PH2; JST_PH_S2B-PH-SM4-TB_1x02-1MP_P2.00mm_Horizontal; MPN C47647; JLCSMT C47647
J4: Spare IO; 4_PIN_THT_Staggered
JP1, JP2: JMP; SolderJumper-2_P1.3mm_Bridged_RoundedPad1.0x1.5mm
K_1, K_9, K_15, K_22, K_113: Encoder_MX; MX_KEYSWITCH_ENCODER
K_2, K_3, K_5, K_6, K_8, K_10, K_11, K_12, K_13, K_14, K_16, K_17, K_18, K_19, K_20, K_23, K_26, K_27, K_28, K_29, K_34, K_35, K_37, K_38, K_39, K_40, K_41, K_42, K_44, K_45, K_46, K_47, K_48, K_49, K_50, K_51, K_52, K_53, K_55, K_56, K_57, K_58, K_59, K_60, K_61, K_62, K_63, K_65, K_67, K_68, K_69, K_70, K_71, K_72, K_73, K_74, K_75, K_77, K_78, K_79, K_80, K_81, K_82, K_83, K_84, K_85, K_86, K_87, K_89, K_90, K_91, K_92, K_93, K_94, K_95, K_96, K_98, K_99, K_100, K_101, K_103, K_104, K_105, K_109, K_110, K_111, K_112, K_114, K_115, K_116, K_117, K_118, K_121: KEYSW; MXOnly-1U-NoLED
K_4, K_7, K_21, K_107: KEYSW; MXOnly-2U-NoLED
K_24, K_25: KEYSW; MXOnly-1U-NoLED-3PIN
K_30, K_36, K_43, K_66: KEYSW; MXOnly-1.25U-NoLED
K_31: KEYSW; MXOnly-1.5U-NoLED-3PIN
K_32: KEYSW; MXOnly-1.75U-NoLED-3PIN
K_33, K_76, K_106: KEYSW; MXOnly-2.25U-NoLED
K_54: KEYSW; MXOnly-2.75U-NoLED
K_64: KEYSW; MXOnly-6.25U-NoLED
K_88, K_97, K_108, K_120: KEYSW; MXOnly-1.5U-NoLED
K_102: KEYSW; MXOnly-1.75U-NoLED
LOGO1: Josh-Details; josh-details
LOGO2: Josh-Logo; josh-johnson-logo-17x3
LOGO3: OSHW Logo; OSHW_Logo_3.6x3.6_F.Mask
Q1: 2N7002; SOT-23; MPN 2N7002; JLCSMT C8545
Q2, Q3: AO3401A; SOT-23; MPN AO3401A; JLCSMT C15127
R1, R10: 806K; R_0603_1608Metric; MPN 0603WAF8063T5E; JLCSMT C23250
R2: 2M; R_0603_1608Metric; MPN 0603WAF2004T5E; JLCSMT C22976
R3, R4, R5, R6, R7, R9: 5K1; R_0603_1608Metric; MPN 0603WAF5101T5E; JLCSMT C23186
R8, R11: 2K; R_0603_1608Metric
SW1: RESET; SW_Push_KMR2; MPN KMR231GLFS; LCSC C99271
U1: nRF52840_holyiot_18010; MPN YJ-18010
U2: SN74LVC1T45DBV; SOT-363_SC-70-6; MPN SN74LVC1T45DBV; JLCSMT C7843
U3: XC6206P332MR; SOT-23; MPN XC6206P332MR; JLCSMT C5446
U4: SRV05-4; SOT-23-6; MPN SRV05-4-P-T7; JLCSMT C85364
U5: TP4057; SOT-23-6; MPN TP4057-42-SOT26-R; JLCSMT C12044

Connections:
+3V3: C19.1, C21.2, J1.5, U1.14 (VDD_nRF), U2.1 (VCCA), U2.5 (DIR), U3.2 (VO)
+5V: C25.1, C26.1, D21.2 (A), D23.2 (A), D24.2 (A), F1.1, Q3.1 (G), R10.1, U1.22 (VBUS), U5.4 (VCC)
+BATT: C20.1, J3.1, Q2.2 (S), Q3.3 (D), R1.1, R6.2, U2.6 (VCCB), U5.3 (BATT)
COL0: K_1.S1, K_2.1 (COL), K_3.1 (COL), K_4.1 (COL), K_5.1 (COL), K_6.1 (COL), K_7.1 (COL), K_8.1 (COL), U1.36 (P0.10)
COL1: K_9.S1, K_10.1 (COL), K_11.1 (COL), K_12.1 (COL), K_13.1 (COL), K_14.1 (COL), U1.5 (P1.15)
COL2: K_15.S1, K_16.1 (COL), K_17.1 (COL), K_18.1 (COL), K_19.1 (COL), K_20.1 (COL), U1.15 (P0.07)
COL3: K_21.1 (COL), K_22.S1, K_23.1 (COL), K_24.1 (COL), K_25.1 (COL), K_26.1 (COL), K_27.1 (COL), U1.16 (P1.09)
COL4: K_28.1 (COL), K_29.1 (COL), K_30.1 (COL), K_31.1 (COL), K_32.1 (COL), K_120.1 (COL), U1.35 (P0.09)
COL5: K_33.1 (COL), K_34.1 (COL), K_35.1 (COL), K_36.1 (COL), K_121.1 (COL), U1.38 (P1.14)
COL6: K_37.1 (COL), K_38.1 (COL), K_39.1 (COL), K_40.1 (COL), K_41.1 (COL), U1.30 (P1.02)
COL7: K_42.1 (COL), K_43.1 (COL), K_44.1 (COL), K_45.1 (COL), K_46.1 (COL), K_47.1 (COL), U1.29 (P1.01)
COL8: K_48.1 (COL), K_49.1 (COL), K_50.1 (COL), K_51.1 (COL), K_52.1 (COL), U1.53 (P0.14)
COL9: K_53.1 (COL), K_54.1 (COL), K_55.1 (COL), K_56.1 (COL), K_57.1 (COL), K_58.1 (COL), U1.28 (P1.03)
COL10: K_59.1 (COL), K_60.1 (COL), K_61.1 (COL), K_62.1 (COL), K_63.1 (COL), K_64.1 (COL), K_66.1 (COL), U1.27 (P1.00)
COL11: K_65.1 (COL), K_67.1 (COL), K_68.1 (COL), K_69.1 (COL), K_70.1 (COL), U1.26 (P0.22)
COL12: K_71.1 (COL), K_72.1 (COL), K_73.1 (COL), K_74.1 (COL), K_75.1 (COL), K_76.1 (COL), U1.39 (P1.12)
COL13: K_77.1 (COL), K_78.1 (COL), K_79.1 (COL), K_80.1 (COL), K_81.1 (COL), U1.47 (P1.07)
COL14: K_82.1 (COL), K_83.1 (COL), K_84.1 (COL), K_85.1 (COL), K_86.1 (COL), K_87.1 (COL), K_88.1 (COL), U1.48 (P1.05)
COL15: K_89.1 (COL), K_90.1 (COL), K_91.1 (COL), K_92.1 (COL), K_93.1 (COL), K_94.1 (COL), U1.34 (P1.06)
COL16: K_95.1 (COL), K_96.1 (COL), K_97.1 (COL), K_98.1 (COL), K_99.1 (COL), K_100.1 (COL), U1.49 (P0.24)
COL17: K_101.1 (COL), K_102.1 (COL), K_103.1 (COL), K_104.1 (COL), K_105.1 (COL), K_106.1 (COL), U1.33 (P1.04)
COL18: K_107.1 (COL), K_108.1 (COL), K_109.1 (COL), K_110.1 (COL), K_111.1 (COL), K_112.1 (COL), U1.50 (P0.20)
COL19: K_113.S1, K_114.1 (COL), K_115.1 (COL), K_116.1 (COL), K_117.1 (COL), K_118.1 (COL), U1.51 (P0.17)
ENC0_A: K_1.A, U1.7 (P0.02)
ENC0_B: K_1.B, U1.8 (P0.28)
ENC1_A: K_9.A, U1.9 (P0.29)
ENC1_B: K_9.B, U1.10 (P0.30)
ENC2_A: K_15.A, U1.17 (P0.12)
ENC2_B: K_15.B, U1.18 (P0.23)
ENC3_A: K_22.A, U1.19 (P0.21)
ENC3_B: K_22.B, U1.20 (P0.19)
ENC4_A: K_113.A, U1.2 (P1.11)
ENC4_B: K_113.B, U1.3 (P1.10)
GND: C1.1, C2.1, C3.1, C4.1, C5.1, C6.1, C7.1, C8.1, C9.1, C10.1, C11.1, C12.1, C13.1, C14.1, C15.1, C16.1, C17.1, C18.1, C19.2, C20.2, C21.1, C22.2, C23.1, C24.1, C25.2, C26.2, C27.1, D1.3 (GND), D2.3 (GND), D3.3 (GND), D4.3 (GND), D5.3 (VSS), D6.3 (VSS), D7.3 (VSS), D8.3 (VSS), D9.3 (VSS), D10.3 (VSS), D11.3 (VSS), D12.3 (VSS), D13.3 (VSS), D14.3 (VSS), D15.3 (VSS), D16.3 (VSS), D17.3 (VSS), D18.3 (VSS), D19.3 (VSS), D20.3 (VSS), J1.3, J2.A1 (GND), J2.A12 (GND), J2.B1 (GND), J2.B12 (GND), J2.S1 (SHIELD), J3.2, J4.4, K_1.C, K_9.C, K_15.C, K_22.C, K_113.C, Q1.2 (S), R2.2, R3.2, R4.1, R7.2, R8.1, R10.2, R11.2, SW1.2, U1.1 (GND), U1.25 (GND), U1.37 (GND), U2.2 (GND), U3.1 (GND), U4.2 (VN), U5.2 (GND)
unnamed: C22.1, D21.1 (K), Q3.2 (S), U3.3 (VI)
unnamed: D1.2 (DOUT), D2.4 (DIN)
unnamed: D1.4 (DIN), D20.2 (DOUT)
unnamed: D2.2 (DOUT), D3.4 (DIN)
unnamed: D3.2 (DOUT), D4.4 (DIN)
unnamed: D5.2 (DOUT), D6.4 (DIN)
unnamed: D5.4 (DIN), D7.2 (DOUT)
unnamed: D6.2 (DOUT), D9.4 (DIN)
unnamed: D7.4 (DIN), D8.2 (DOUT)
unnamed: D8.4 (DIN), D10.2 (DOUT)
unnamed: D10.4 (DIN), D12.2 (DOUT)
unnamed: D11.2 (DOUT), D13.4 (DIN)
unnamed: D9.2 (DOUT), D11.4 (DIN)
unnamed: D12.4 (DIN), D14.2 (DOUT)
unnamed: D13.2 (DOUT), D15.4 (DIN)
unnamed: D14.4 (DIN), D16.2 (DOUT)
unnamed: D15.2 (DOUT), D17.4 (DIN)
unnamed: D16.4 (DIN), D18.2 (DOUT)
unnamed: D17.2 (DOUT), D20.4 (DIN)
unnamed: D18.4 (DIN), D19.2 (DOUT)
unnamed: D22.1 (K), R11.1
unnamed: D23.1 (K), JP1.1
unnamed: D24.1 (K), JP2.1
unnamed: D_1.2 (A), K_113.S2
unnamed: D_2.2 (A), K_114.2 (ROW)
unnamed: D_3.2 (A), K_115.2 (ROW)
unnamed: D_4.2 (A), K_116.2 (ROW)
unnamed: D_5.2 (A), K_118.2 (ROW)
unnamed: D_6.2 (A), K_117.2 (ROW)
unnamed: D_7.2 (A), K_107.2 (ROW), K_110.2 (ROW)
unnamed: D_8.2 (A), K_109.2 (ROW)
unnamed: D_9.2 (A), K_112.2 (ROW)
unnamed: D_10.2 (A), K_111.2 (ROW)
unnamed: D_11.2 (A), K_108.2 (ROW)
unnamed: D_12.2 (A), K_106.2 (ROW)
unnamed: D_13.2 (A), K_103.2 (ROW)
unnamed: D_14.2 (A), K_105.2 (ROW)
unnamed: D_15.2 (A), K_102.2 (ROW)
unnamed: D_16.2 (A), K_101.2 (ROW)
unnamed: D_17.2 (A), K_104.2 (ROW)
unnamed: D_18.2 (A), K_98.2 (ROW)
unnamed: D_19.2 (A), K_97.2 (ROW), K_100.2 (ROW)
unnamed: D_20.2 (A), K_99.2 (ROW)
unnamed: D_21.2 (A), K_96.2 (ROW)
unnamed: D_22.2 (A), K_95.2 (ROW)
unnamed: D_23.2 (A), K_94.2 (ROW)
unnamed: D_24.2 (A), K_91.2 (ROW)
unnamed: D_25.2 (A), K_92.2 (ROW)
unnamed: D_26.2 (A), K_93.2 (ROW)
unnamed: D_27.2 (A), K_90.2 (ROW)
unnamed: D_28.2 (A), K_89.2 (ROW)
unnamed: D_29.2 (A), K_87.2 (ROW)
unnamed: D_30.2 (A), K_86.2 (ROW), K_88.2 (ROW)
unnamed: D_31.2 (A), K_84.2 (ROW)
unnamed: D_32.2 (A), K_85.2 (ROW)
unnamed: D_33.2 (A), K_83.2 (ROW)
unnamed: D_34.2 (A), K_82.2 (ROW)
unnamed: D_35.2 (A), K_81.2 (ROW)
unnamed: D_36.2 (A), K_79.2 (ROW)
unnamed: D_37.2 (A), K_80.2 (ROW)
unnamed: D_38.2 (A), K_78.2 (ROW)
unnamed: D_39.2 (A), K_77.2 (ROW)
unnamed: D_40.2 (A), K_76.2 (ROW)
unnamed: D_41.2 (A), K_75.2 (ROW)
unnamed: D_42.2 (A), K_73.2 (ROW)
unnamed: D_43.2 (A), K_74.2 (ROW)
unnamed: D_44.2 (A), K_72.2 (ROW)
unnamed: D_45.2 (A), K_71.2 (ROW)
unnamed: D_46.2 (A), K_70.2 (ROW)
unnamed: D_47.2 (A), K_68.2 (ROW)
unnamed: D_48.2 (A), K_69.2 (ROW)
unnamed: D_49.2 (A), K_67.2 (ROW)
unnamed: D_50.2 (A), K_64.2 (ROW), K_66.2 (ROW)
unnamed: D_51.2 (A), K_65.2 (ROW)
unnamed: D_52.2 (A), K_63.2 (ROW)
unnamed: D_53.2 (A), K_61.2 (ROW)
unnamed: D_54.2 (A), K_62.2 (ROW)
unnamed: D_55.2 (A), K_60.2 (ROW)
unnamed: D_56.2 (A), K_59.2 (ROW)
unnamed: D_57.2 (A), K_58.2 (ROW)
unnamed: D_58.2 (A), K_56.2 (ROW)
unnamed: D_59.2 (A), K_57.2 (ROW)
unnamed: D_60.2 (A), K_55.2 (ROW)
unnamed: D_61.2 (A), K_54.2 (ROW)
unnamed: D_62.2 (A), K_53.2 (ROW)
unnamed: D_63.2 (A), K_52.2 (ROW)
unnamed: D_64.2 (A), K_50.2 (ROW)
unnamed: D_65.2 (A), K_51.2 (ROW)
unnamed: D_66.2 (A), K_49.2 (ROW)
unnamed: D_67.2 (A), K_48.2 (ROW)
unnamed: D_68.2 (A), K_47.2 (ROW)
unnamed: D_69.2 (A), K_45.2 (ROW)
unnamed: D_70.2 (A), K_46.2 (ROW)
unnamed: D_71.2 (A), K_44.2 (ROW)
unnamed: D_72.2 (A), K_43.2 (ROW)
unnamed: D_73.2 (A), K_42.2 (ROW)
unnamed: D_74.2 (A), K_41.2 (ROW)
unnamed: D_75.2 (A), K_39.2 (ROW)
unnamed: D_76.2 (A), K_40.2 (ROW)
unnamed: D_77.2 (A), K_38.2 (ROW)
unnamed: D_78.2 (A), K_37.2 (ROW)
unnamed: D_79.2 (A), K_36.2 (ROW), K_121.2 (ROW)
unnamed: D_80.2 (A), K_34.2 (ROW)
unnamed: D_81.2 (A), K_35.2 (ROW)
unnamed: D_82.2 (A), K_33.2 (ROW)
unnamed: D_83.2 (A), K_32.2 (ROW)
unnamed: D_84.2 (A), K_31.2 (ROW)
unnamed: D_85.2 (A), K_30.2 (ROW), K_120.2 (ROW)
unnamed: D_86.2 (A), K_28.2 (ROW)
unnamed: D_87.2 (A), K_29.2 (ROW)
unnamed: D_88.2 (A), K_23.2 (ROW)
unnamed: D_89.2 (A), K_21.2 (ROW), K_27.2 (ROW)
unnamed: D_90.2 (A), K_26.2 (ROW)
unnamed: D_91.2 (A), K_24.2 (ROW)
unnamed: D_92.2 (A), K_25.2 (ROW)
unnamed: D_93.2 (A), K_22.S2
unnamed: D_94.2 (A), K_17.2 (ROW)
unnamed: D_95.2 (A), K_18.2 (ROW)
unnamed: D_96.2 (A), K_16.2 (ROW)
unnamed: D_97.2 (A), K_19.2 (ROW)
unnamed: D_98.2 (A), K_20.2 (ROW)
unnamed: D_99.2 (A), K_15.S2
unnamed: D_100.2 (A), K_11.2 (ROW)
unnamed: D_101.2 (A), K_12.2 (ROW)
unnamed: D_102.2 (A), K_13.2 (ROW)
unnamed: D_103.2 (A), K_1.S2
unnamed: D_104.2 (A), K_10.2 (ROW)
unnamed: D_105.2 (A), K_3.2 (ROW)
unnamed: D_106.2 (A), K_4.2 (ROW), K_5.2 (ROW)
unnamed: D_107.2 (A), K_14.2 (ROW)
unnamed: D_108.2 (A), K_6.2 (ROW)
unnamed: D_109.2 (A), K_9.S2
unnamed: D_110.2 (A), K_2.2 (ROW)
unnamed: D_111.2 (A), K_7.2 (ROW), K_8.2 (ROW)
unnamed: J2.A5 (CC1), R4.2
unnamed: J2.B5 (CC2), R7.1
unnamed: JP1.2, R9.2
unnamed: JP2.2, R5.2
unnamed: Q1.3 (D), Q2.1 (G), R6.1
unnamed: R5.1, U5.1 (nCHRG)
unnamed: R8.2, U5.6 (PROG)
unnamed: R9.1, U5.5 (nSTDBY)
ROW0: D_1.1 (K), D_8.1 (K), D_13.1 (K), D_18.1 (K), D_24.1 (K), D_31.1 (K), D_36.1 (K), D_42.1 (K), D_47.1 (K), D_53.1 (K), D_58.1 (K), D_64.1 (K), D_69.1 (K), D_75.1 (K), D_80.1 (K), D_86.1 (K), D_93.1 (K), D_99.1 (K), D_103.1 (K), D_109.1 (K), U1.46 (P0.26)
ROW1: D_2.1 (K), D_7.1 (K), D_17.1 (K), D_20.1 (K), D_25.1 (K), D_32.1 (K), D_37.1 (K), D_43.1 (K), D_48.1 (K), D_54.1 (K), D_59.1 (K), D_65.1 (K), D_70.1 (K), D_76.1 (K), D_81.1 (K), D_87.1 (K), D_88.1 (K), D_96.1 (K), D_104.1 (K), D_110.1 (K), U1.45 (P0.06)
ROW2: D_3.1 (K), D_11.1 (K), D_16.1 (K), D_22.1 (K), D_28.1 (K), D_34.1 (K), D_39.1 (K), D_45.1 (K), D_51.1 (K), D_56.1 (K), D_62.1 (K), D_67.1 (K), D_73.1 (K), D_78.1 (K), D_84.1 (K), D_91.1 (K), D_94.1 (K), D_100.1 (K), D_105.1 (K), U1.43 (P0.27)
ROW3: D_4.1 (K), D_12.1 (K), D_21.1 (K), D_27.1 (K), D_33.1 (K), D_38.1 (K), D_44.1 (K), D_49.1 (K), D_55.1 (K), D_60.1 (K), D_66.1 (K), D_71.1 (K), D_77.1 (K), D_83.1 (K), D_92.1 (K), D_95.1 (K), D_101.1 (K), D_106.1 (K), U1.44 (P0.08)
ROW4: D_6.1 (K), D_10.1 (K), D_15.1 (K), D_23.1 (K), D_29.1 (K), D_35.1 (K), D_41.1 (K), D_46.1 (K), D_52.1 (K), D_57.1 (K), D_63.1 (K), D_68.1 (K), D_74.1 (K), D_82.1 (K), D_90.1 (K), D_97.1 (K), D_102.1 (K), D_108.1 (K), U1.41 (P0.11)
ROW5: D_5.1 (K), D_9.1 (K), D_14.1 (K), D_19.1 (K), D_26.1 (K), D_30.1 (K), D_40.1 (K), D_50.1 (K), D_61.1 (K), D_72.1 (K), D_79.1 (K), D_85.1 (K), D_89.1 (K), D_98.1 (K), D_107.1 (K), D_111.1 (K), U1.40 (P0.25)
SPARE_0: J4.1, U1.54 (P0.13)
SPARE_1: J4.2, U1.55 (P0.16)
SPARE_2: J4.3, U1.42 (P1.08)
SWDCLK: J1.4, U1.31 (SWDCLK)
SWDIO: J1.2, U1.32 (SWDIO)
UG_DAT: U1.13 (P0.05), U2.3 (A)
UG_DAT_VBATT: D19.4 (DIN), U2.4 (B)
UG_EN: Q1.1 (G), R3.1, U1.12 (P0.04)
UG_VPWR: C1.2, C2.2, C3.2, C4.2, C5.2, C6.2, C7.2, C8.2, C9.2, C10.2, C11.2, C12.2, C13.2, C14.2, C15.2, C16.2, C17.2, C18.2, C23.2, C27.2, D1.1 (VDD), D2.1 (VDD), D3.1 (VDD), D4.1 (VDD), D5.1 (VDD), D6.1 (VDD), D7.1 (VDD), D8.1 (VDD), D9.1 (VDD), D10.1 (VDD), D11.1 (VDD), D12.1 (VDD), D13.1 (VDD), D14.1 (VDD), D15.1 (VDD), D16.1 (VDD), D17.1 (VDD), D18.1 (VDD), D19.1 (VDD), D20.1 (VDD), Q2.3 (D)
USB_D+: J2.A6 (D+), J2.B6 (D+), U1.24 (D+), U4.3 (IO2)
USB_D-: J2.A7 (D-), J2.B7 (D-), U1.23 (D-), U4.4 (IO3)
USR_LED: D22.2 (A), U1.4 (P1.13)
VBUS: C24.2, F1.2, J2.A4 (VBUS), J2.A9 (VBUS), J2.B4 (VBUS), J2.B9 (VBUS), U4.5 (VP)
VSENSE: R1.2, R2.1, U1.11 (P0.31)
nRST: J1.1, SW1.1, U1.21 (P0.18/RESET)

Notes on the sheet:
USB
Cut to disable status LEDs
Charge
2K = 400mA Charge
Power Regulation
Keyboard Matrix
nRF52840
Leave NC for SPI Driver
Spare
Programming
High Side Disable
3v3 -> VBATT logic shift
Logos / Silk
Stopping ERC Errors
Underglow LEDs
Status LEDs
